thekonon/WritingRobot/01_Doc/Img/Board/Board_scheme_silk_on.png

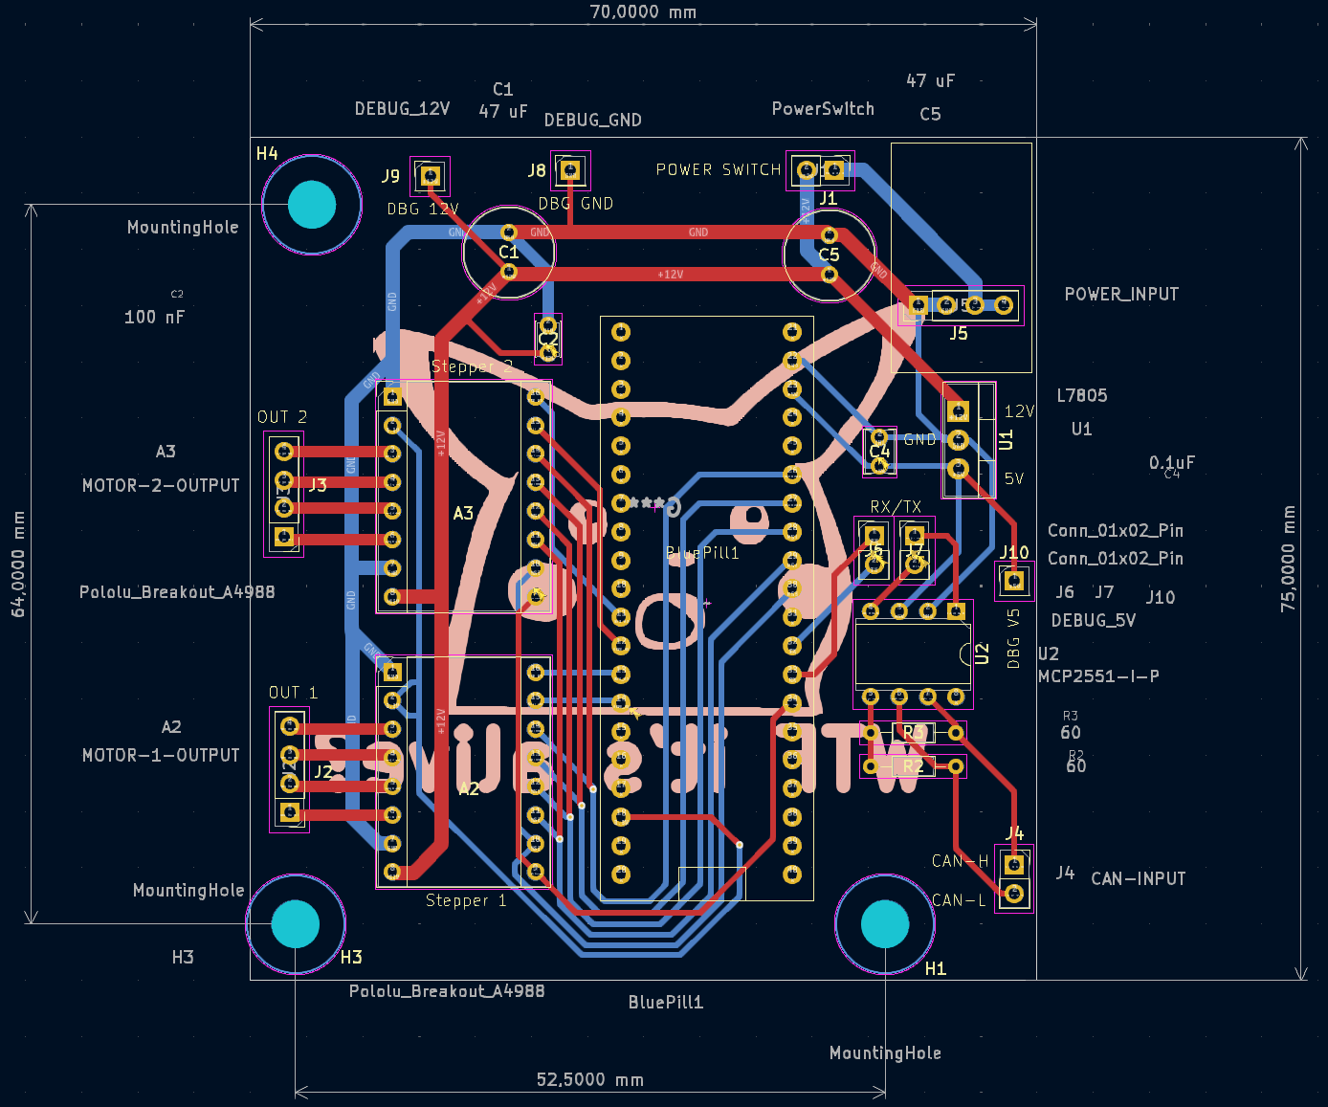
01_Doc/Img/Board/Board_scheme_silk_on.png
