thekonon/WritingRobot/01_Doc/Img/Computation/comp.png

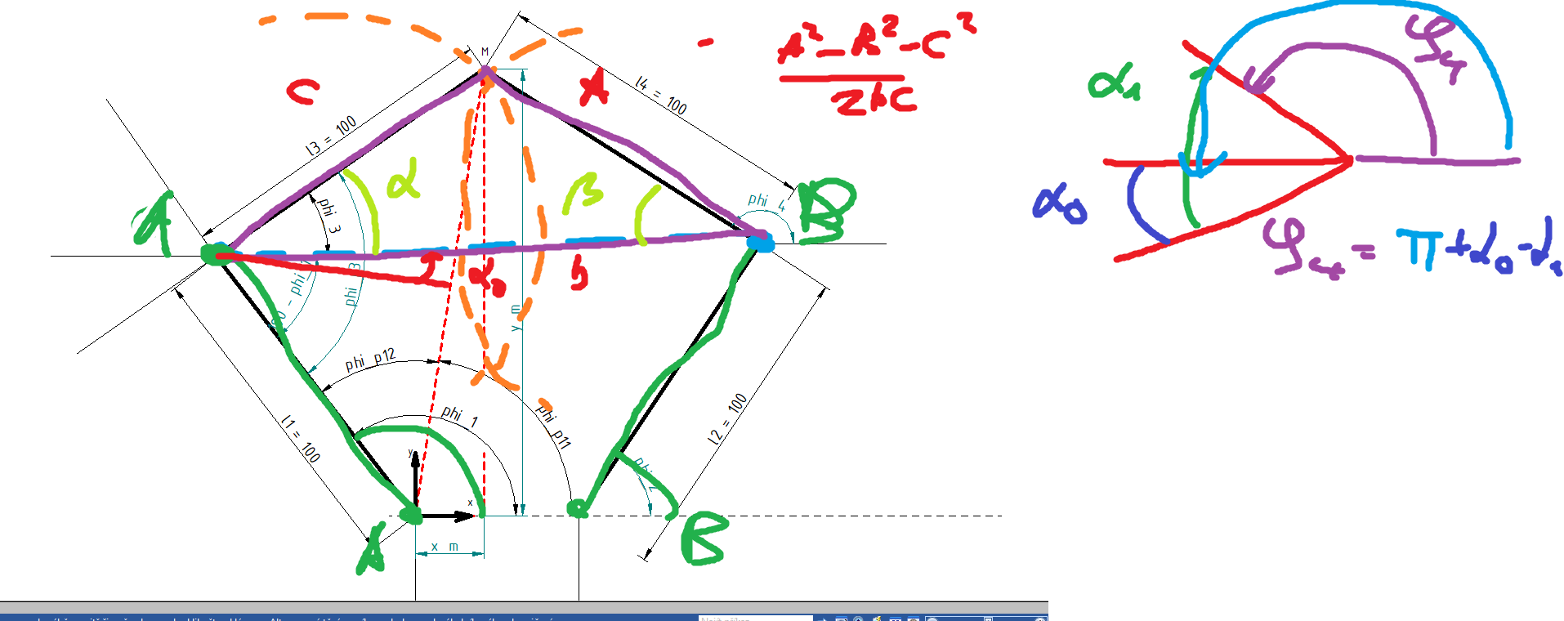
01_Doc/Img/Computation/comp.png
