thekonon/WritingRobot/01_Doc/Img/Computation/comp_2.png

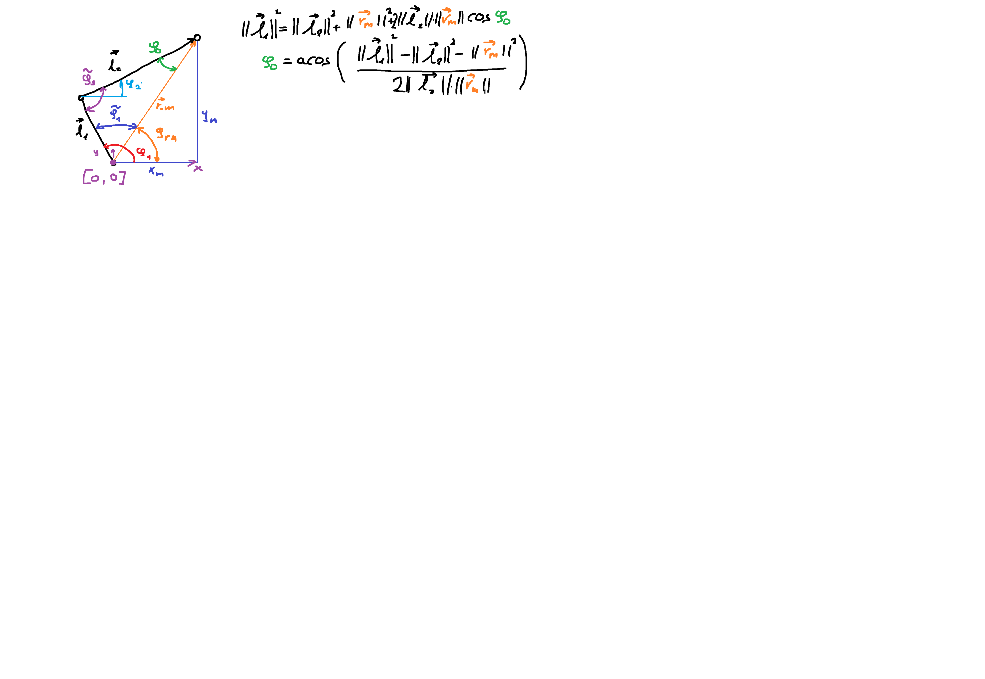
01_Doc/Img/Computation/comp_2.png
