thekonon/WritingRobot/01_Doc/Img/Computation/Comp_new_2.png

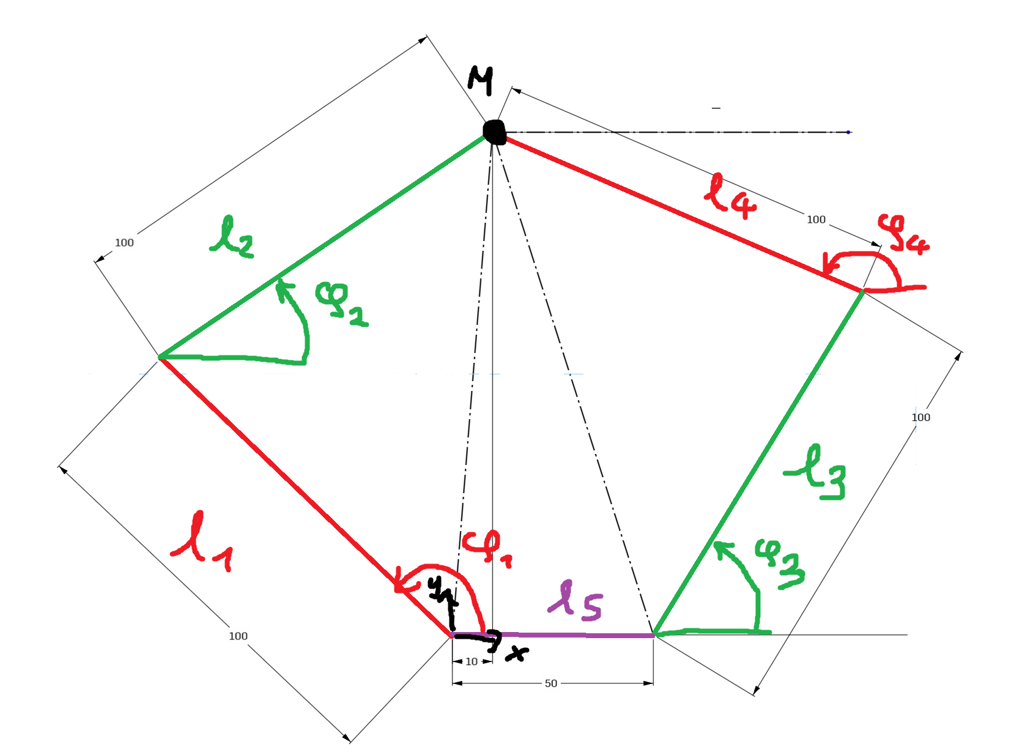
01_Doc/Img/Computation/Comp_new_2.png
