thekonon/WritingRobot/01_Doc/Img/Computation/Comp_new_3.png

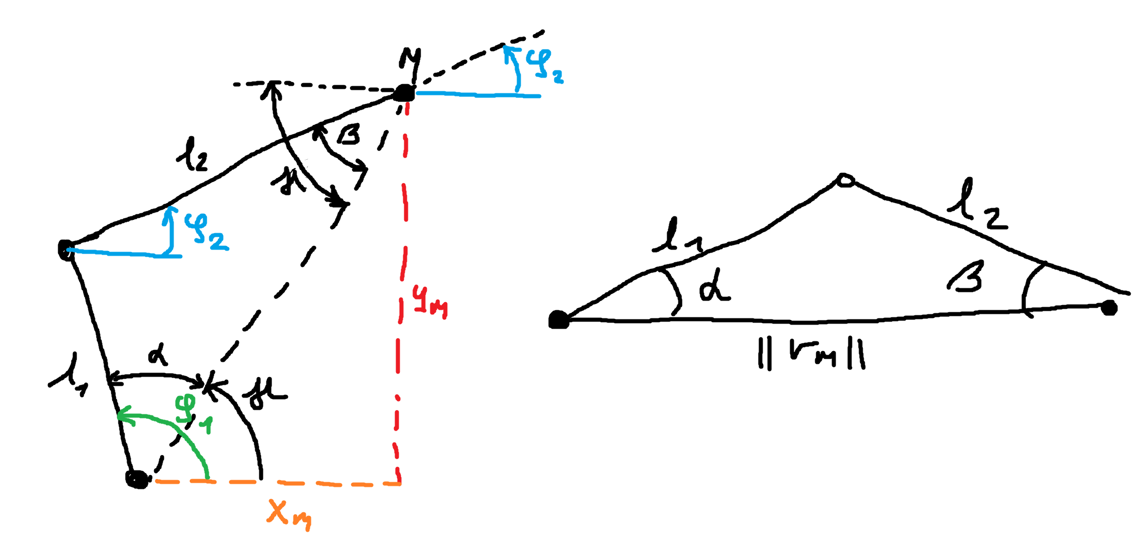
01_Doc/Img/Computation/Comp_new_3.png
