thekonon/WritingRobot/01_Doc/Img/Computation/TCurve/Comparison.png

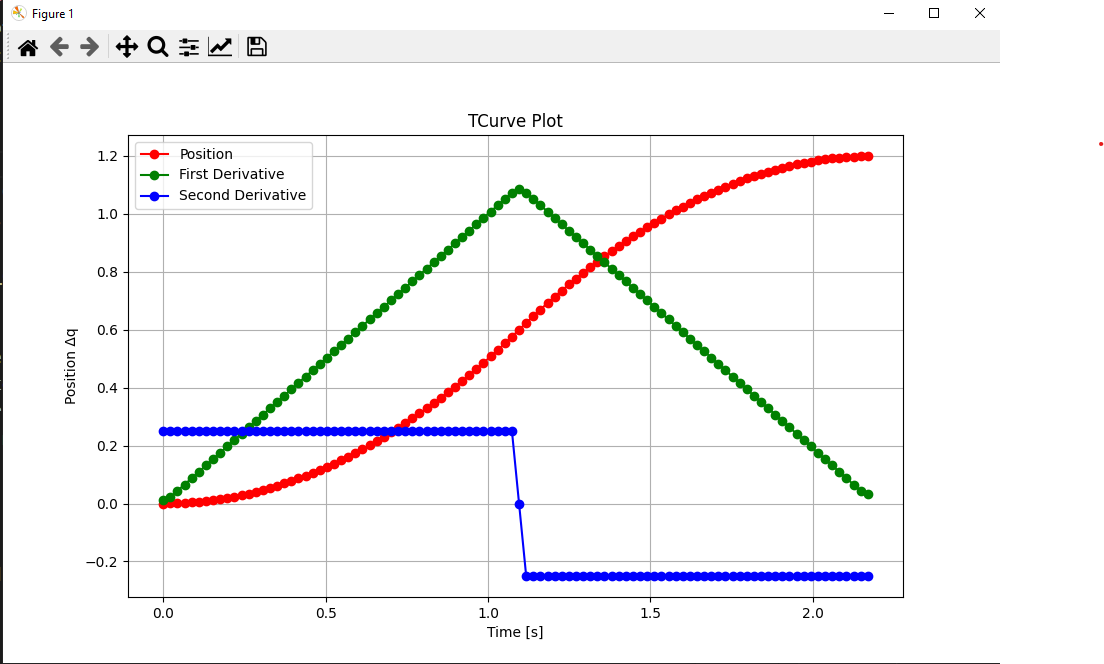
01_Doc/Img/Computation/TCurve/Comparison.png
