thekonon/WritingRobot/01_Doc/Img/Computation/Traectory/comp_1.png

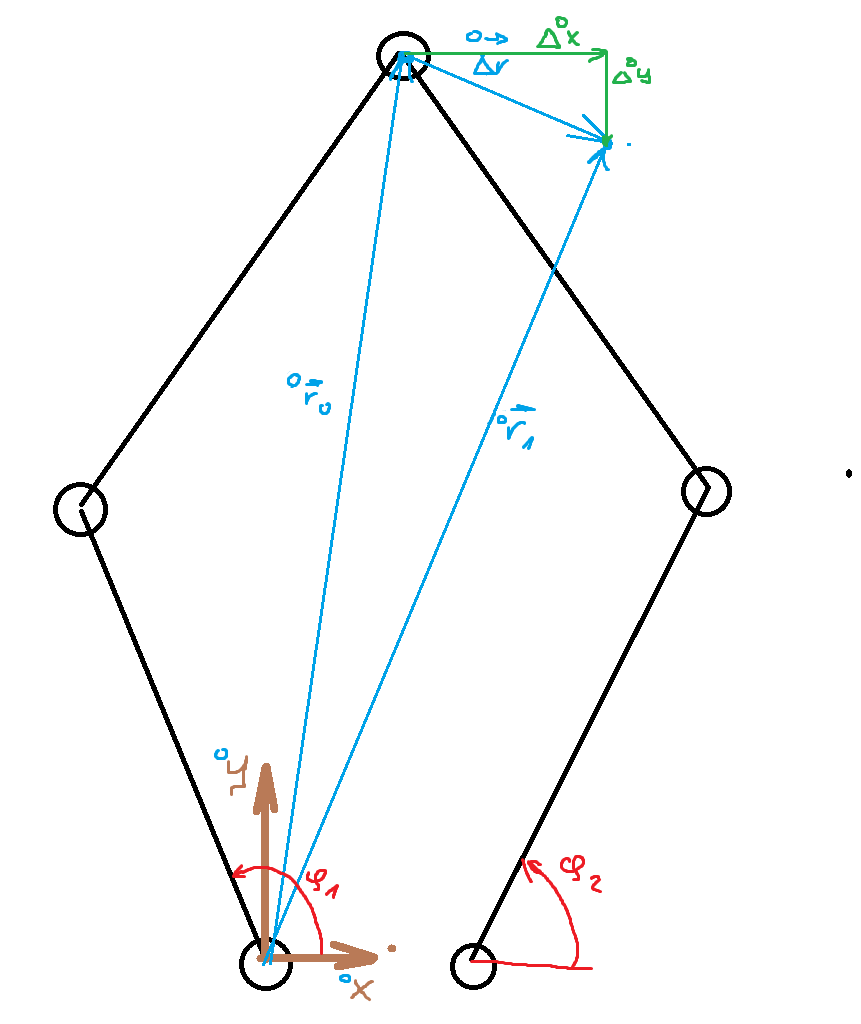
01_Doc/Img/Computation/Traectory/comp_1.png
