thekonon/WritingRobot/01_Doc/Img/Electrical/Arduino.png

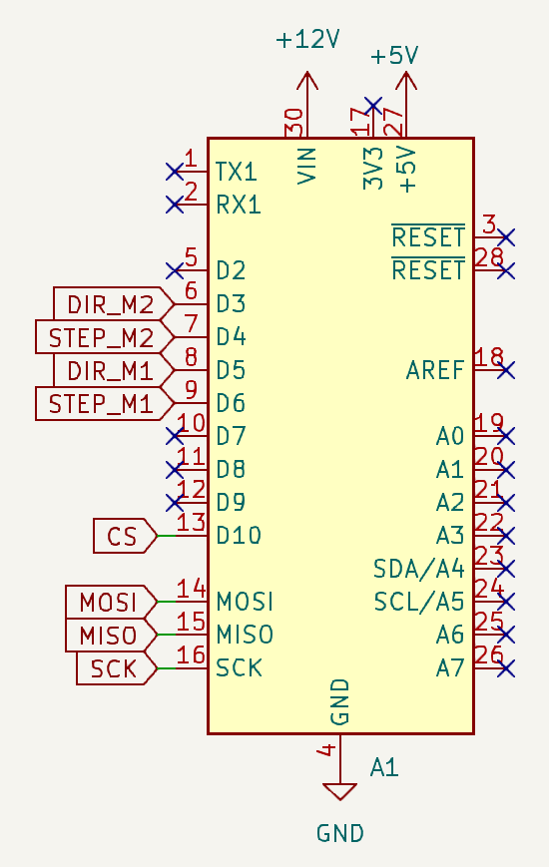
01_Doc/Img/Electrical/Arduino.png
