thekonon/WritingRobot/03_SW/1_ControlApp/gui/constants.py

from typing import List, Tuple

class App:
    APP_WIDTH: int = 900
    APP_HEIGHT: int = 800

class Robot:
    LENGTHS: Tuple[float, float, float, float, float] = \
        (
            80.0, #l1
            90.0, #l2
            100.0, #l3
            110.0, #l4
            50.0  #l5
        )
    INIT_END_POINT: List[float] = \
        [
            25,
            150
        ]

class Test:
    test: int = 100
